LucasGabrielfl0/Cubesat-Hardware/Kicad_Libraries/Models_3D/STM32F411CEU6/BlackPill_F401v31.step

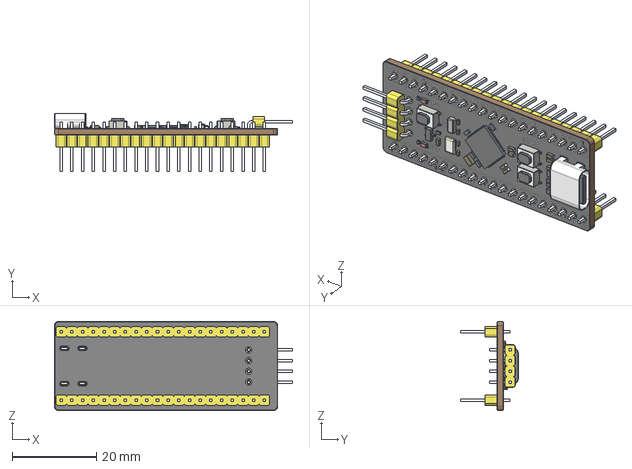
[picture p15: CAD file, 2026-04-24]
Kicad_Libraries/Models_3D/STM32F411CEU6/BlackPill_F401v31.step
56.5 x 13.7 x 21.2 mm
