LucasGabrielfl0/Cubesat-Hardware/Kicad_Libraries/Models_3D/Switch/ss12d06.stp

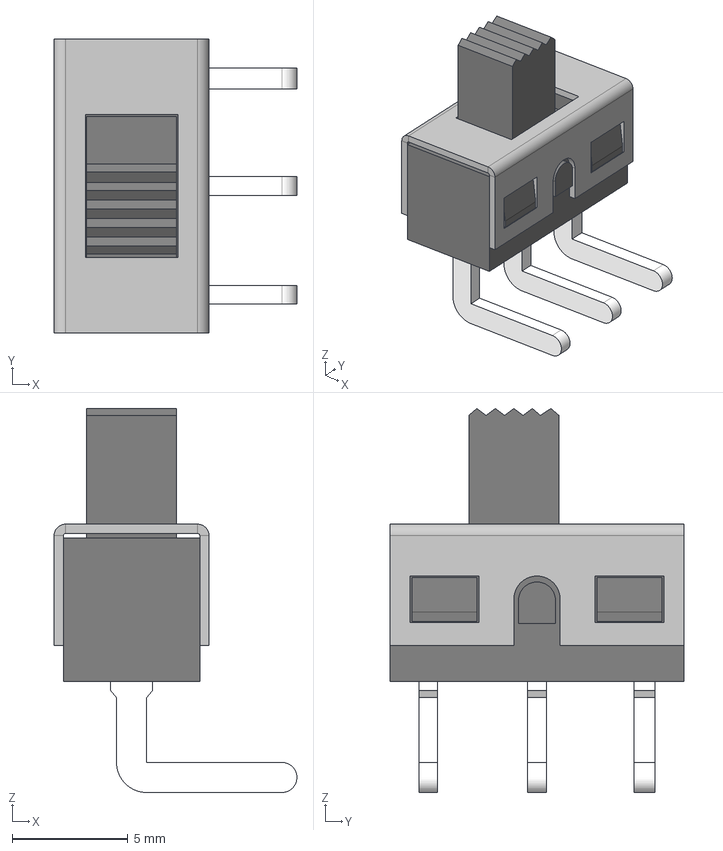
[picture p16: CAD file, 2026-06-01]
Kicad_Libraries/Models_3D/Switch/ss12d06.stp
10.5 x 12.7 x 16.6 mm
