LucasGabrielfl0/Cubesat-Hardware/Kicad_Libraries/Models_3D/Buck_Converter/XL4015 StepDown DC-DC 5A (CC-CV) v1.step

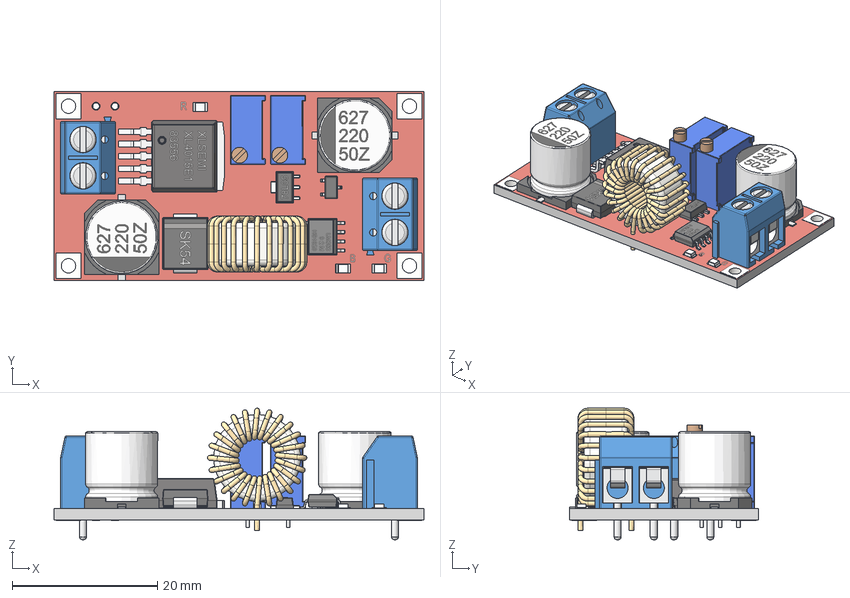
[picture p17: CAD file, 2026-05-25]
Kicad_Libraries/Models_3D/Buck_Converter/XL4015 StepDown DC-DC 5A (CC-CV) v1.step
51.0 x 26.0 x 18.1 mm
Basetta
DG301-5.0-02 v1 x 2
CAPACITOR 10x10 SMD v1 x 2
Trimpot 3296W v1 x 2
DO-214AB v1
XL4015 TO263-5-1 v1
LM358 SOIC08 v1
Toro
Spira x 22
SpiraCodA
SpiraCpdB
UPC78L08T-E1-AZ
SC-59A v1
LED v1 x 3
