LucasGabrielfl0/Cubesat-Hardware/Kicad_Libraries/Models_3D/Electrolytic_Capacitor/Electrolytic_Capacitor.step

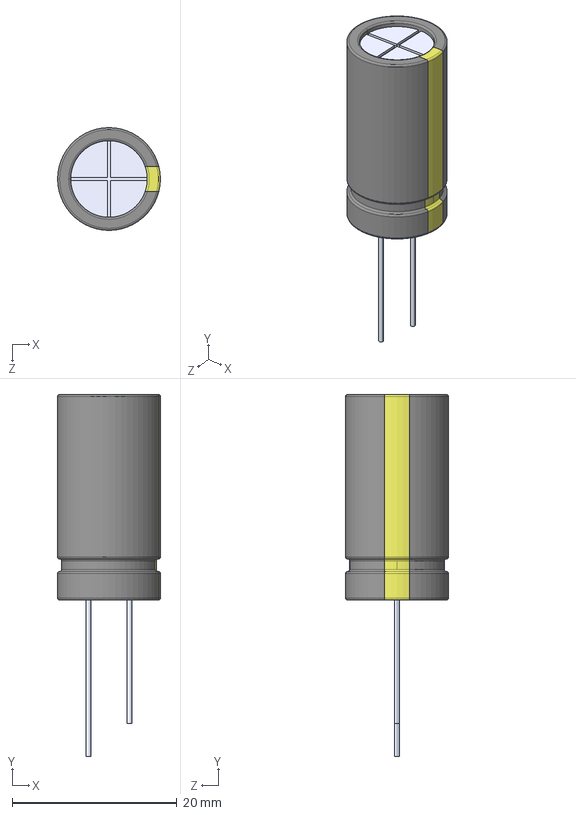
[picture p18: CAD file, 2026-05-12]
Kicad_Libraries/Models_3D/Electrolytic_Capacitor/Electrolytic_Capacitor.step
12.5 x 44.0 x 12.5 mm
