LucasGabrielfl0/Cubesat-Hardware/Kicad_Libraries/Models_3D/GPS_NEO6M/GY-NEO6MV2-noAnt.step

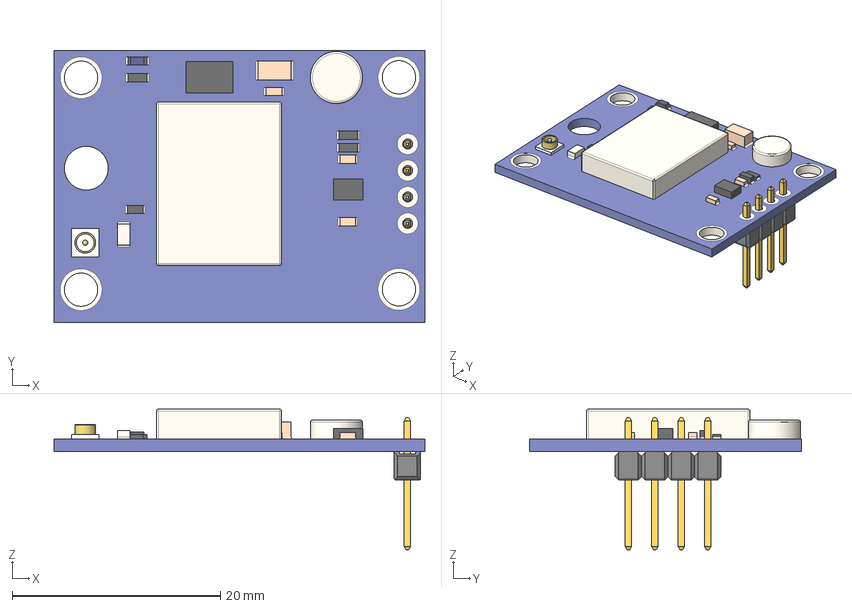
[picture p19: CAD file, 2026-04-24]
Kicad_Libraries/Models_3D/GPS_NEO6M/GY-NEO6MV2-noAnt.step
35.6 x 26.1 x 13.5 mm
Pin Header 1x4 TH Pitch 2.54mm
