LucasGabrielfl0/Cubesat-Hardware/Kicad_Libraries/Models_3D/Others/SS12D10_90_Degree.STEP

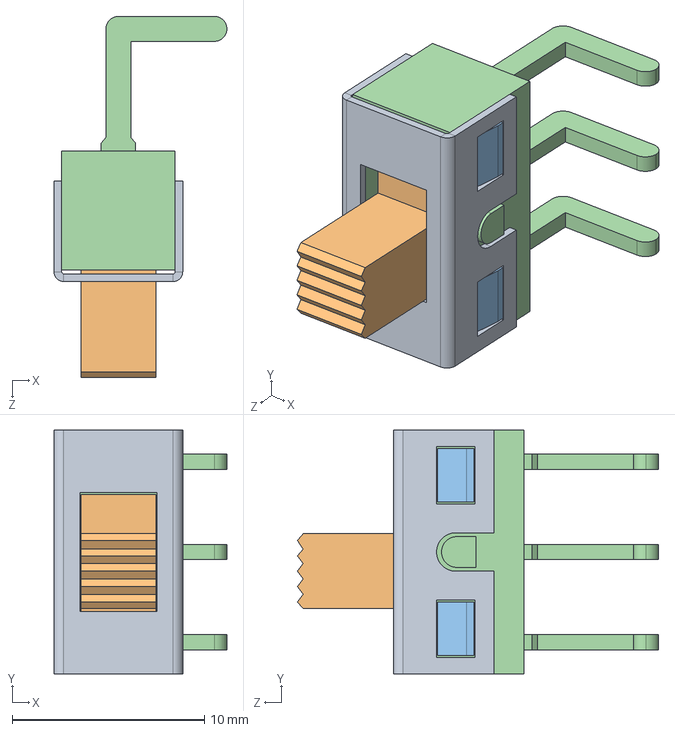
[picture p20: CAD file, 2026-05-26]
Kicad_Libraries/Models_3D/Others/SS12D10_90_Degree.STEP
9.00 x 12.7 x 18.8 mm
