LucasGabrielfl0/Cubesat-Hardware/Kicad_Libraries/Models_3D/BATTERY_PACK_18650/Hold_18650-4p_smd.stp

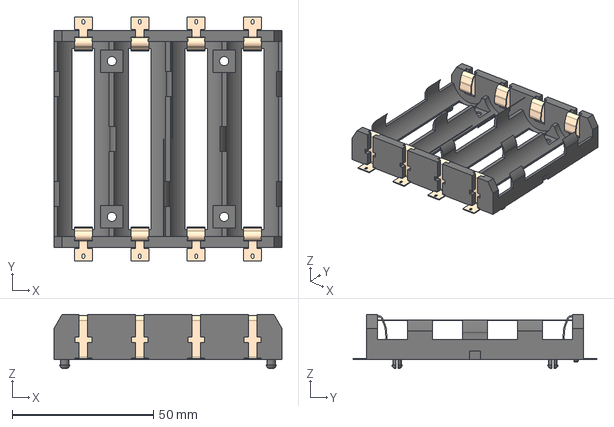
[picture p21: CAD file, 2026-04-24]
Kicad_Libraries/Models_3D/BATTERY_PACK_18650/Hold_18650-4p_smd.stp
80.8 x 86.4 x 19.3 mm
