LucasGabrielfl0/Cubesat-Hardware/Kicad_Libraries/Models_3D/Buck_Converter/LM2596 DC-DC Buck Converter Module.stp

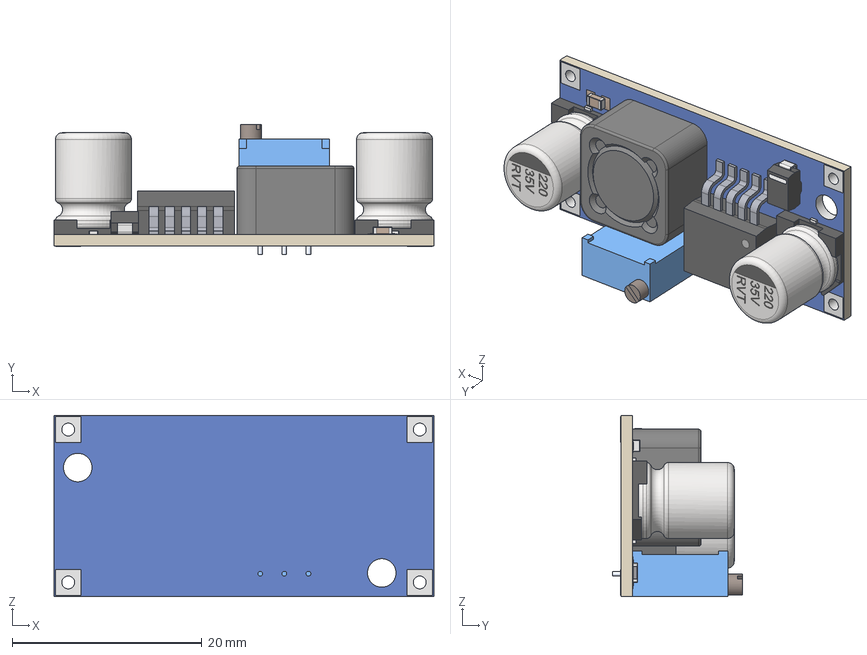
[picture p22: CAD file, 2026-04-24]
Kicad_Libraries/Models_3D/Buck_Converter/LM2596 DC-DC Buck Converter Module.stp
40.0 x 13.7 x 19.1 mm
CAPSMD220-35 x 2
Diode SMA
solder_hole x 4
