LucasGabrielfl0/Cubesat-Hardware/Kicad_Libraries/Models_3D/Electrolytic_Capacitor/0.22uF 50V electr 5 x11mm -P.diameter 2.5 mm-Black-White.stp

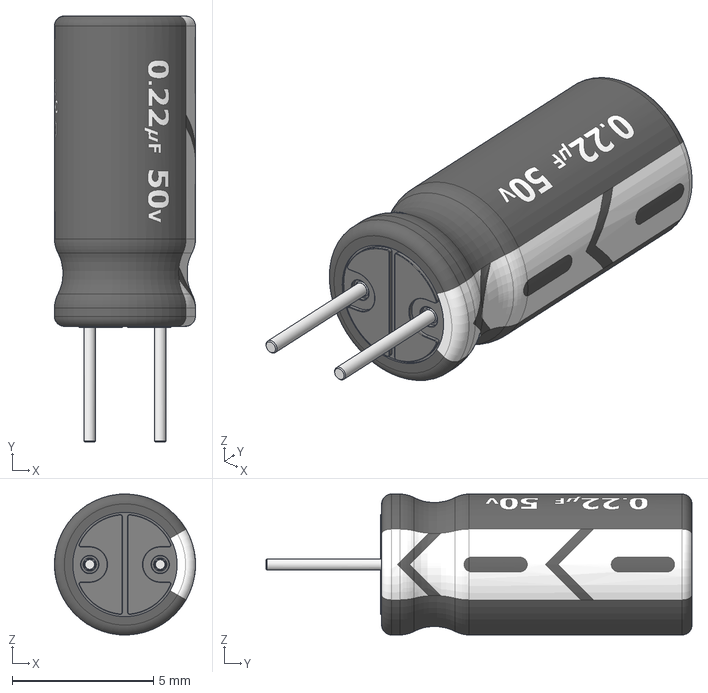
[picture p23: CAD file, 2026-05-12]
Kicad_Libraries/Models_3D/Electrolytic_Capacitor/0.22uF 50V electr 5 x11mm -P.diameter 2.5 mm-Black-White.stp
5.00 x 15.1 x 4.99 mm
