LucasGabrielfl0/Cubesat-Hardware/Kicad_Libraries/Models_3D/BATTERY_PACK_18650/Battery18650_2S.step

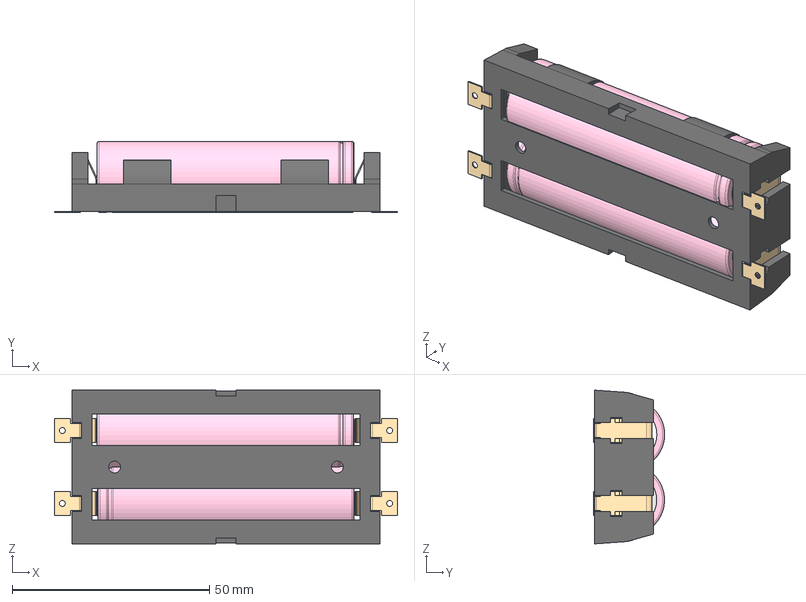
[picture p24: CAD file, 2026-04-24]
Kicad_Libraries/Models_3D/BATTERY_PACK_18650/Battery18650_2S.step
87.0 x 18.1 x 39.0 mm
Battery Holder
Battery-Holder_Metal-Lead x 4
