LucasGabrielfl0/Cubesat-Hardware/Kicad_Libraries/Models_3D/Others/kcd1_a.step

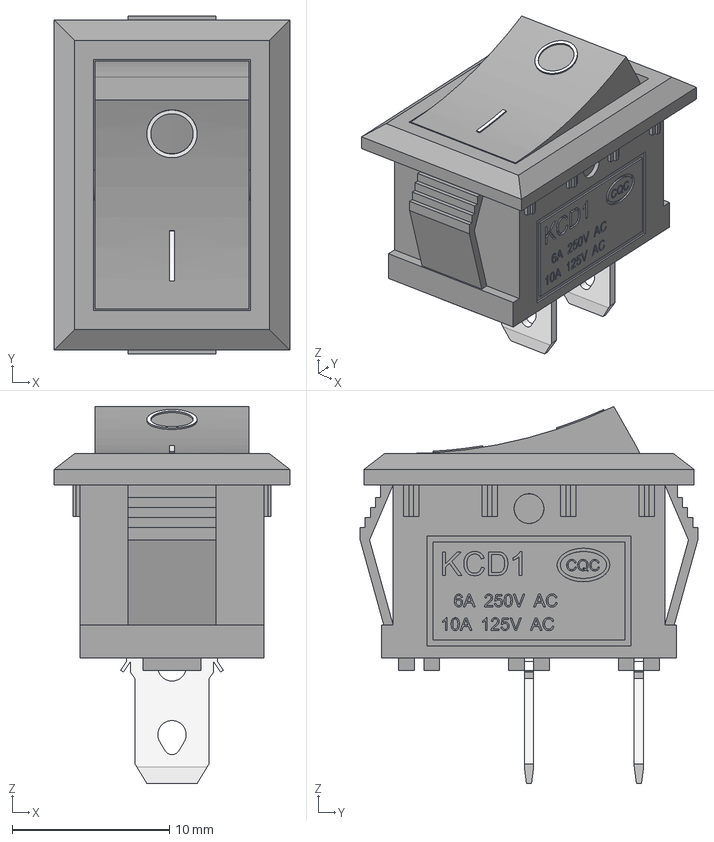
[picture p25: CAD file, 2026-05-25]
Kicad_Libraries/Models_3D/Others/kcd1_a.step
15.0 x 21.5 x 24.0 mm
Blade_001
Blade_002
Base_w_text
knob001
