LucasGabrielfl0/Cubesat-Hardware/Kicad_Libraries/Models_3D/Others/LED 3mm Blue 21mm Leads.step

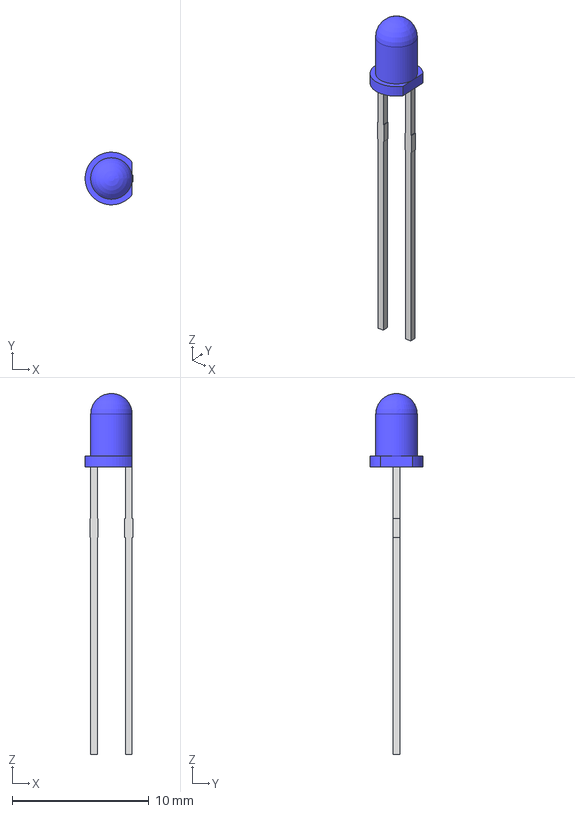
[picture p26: CAD file, 2026-05-12]
Kicad_Libraries/Models_3D/Others/LED 3mm Blue 21mm Leads.step
3.50 x 3.85 x 26.4 mm
LEDBody
Lead1Body
Lead2Body
