LucasGabrielfl0/Cubesat-Hardware/Kicad_Libraries/Models_3D/BATTERY_PACK_18650/BatteryPack_4S.step

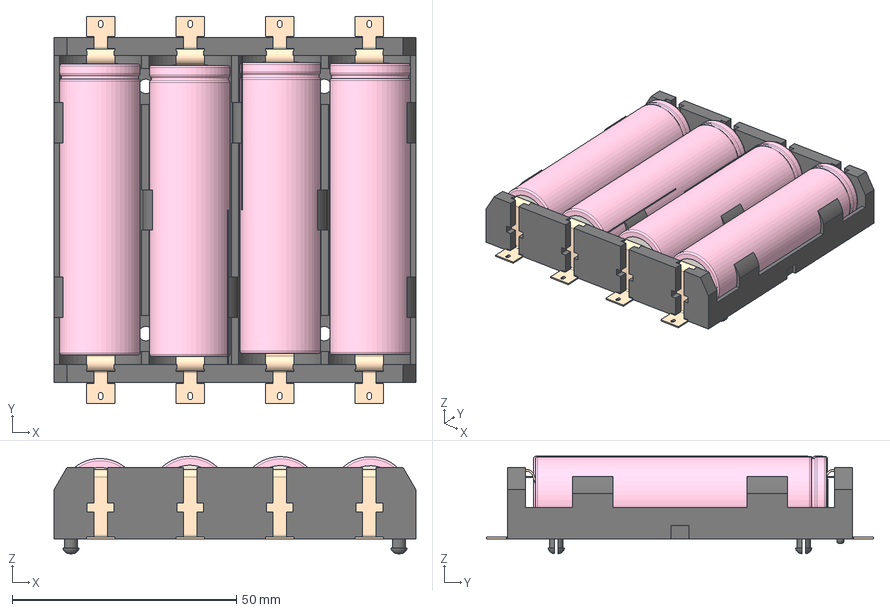
[picture p27: CAD file, 2026-04-24]
Kicad_Libraries/Models_3D/BATTERY_PACK_18650/BatteryPack_4S.step
80.8 x 86.4 x 21.8 mm
Hold_18650_Con_smd x 8
Hold_18650-4p_smd
