LucasGabrielfl0/Cubesat-Hardware/Kicad_Libraries/Models_3D/Others/Led 5mm green_.step

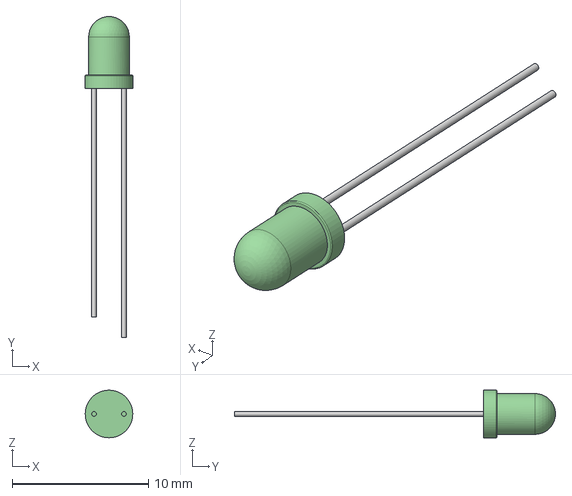
[picture p28: CAD file, 2026-04-24]
Kicad_Libraries/Models_3D/Others/Led 5mm green_.step
3.50 x 23.6 x 3.50 mm
