LucasGabrielfl0/Cubesat-Hardware/Kicad_Libraries/Models_3D/BATTERY_PACK_18650/BLM Blossom Electronics STM THM FOR 18650 Battery Holder With Battery V1.2.STEP

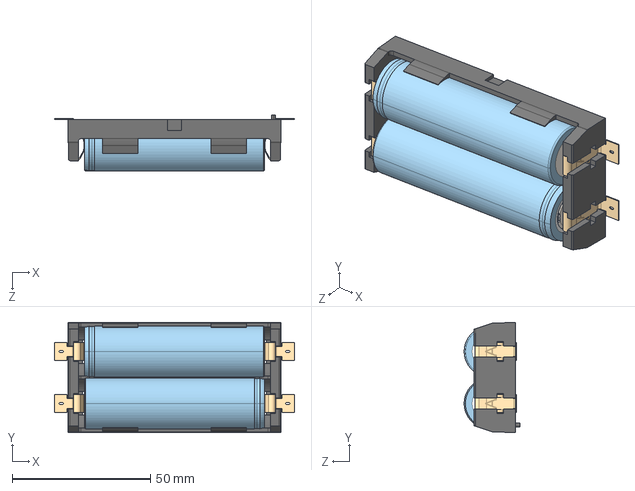
[picture p29: CAD file, 2026-04-24]
Kicad_Libraries/Models_3D/BATTERY_PACK_18650/BLM Blossom Electronics STM THM FOR 18650 Battery Holder With Battery V1.2.STEP
86.8 x 39.8 x 20.2 mm
