LucasGabrielfl0/Cubesat-Hardware/Kicad_Libraries/Models_3D/Others/Led 5mm red_.step

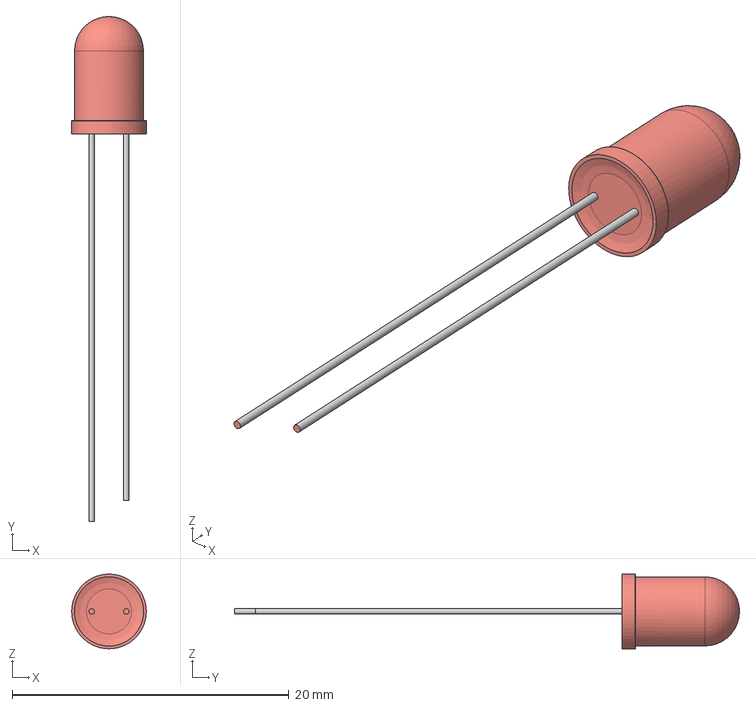
[picture p30: CAD file, 2026-04-24]
Kicad_Libraries/Models_3D/Others/Led 5mm red_.step
5.40 x 36.5 x 5.39 mm
