LucasGabrielfl0/Cubesat-Hardware/Kicad_Libraries/Models_3D/Others/Wippschalter Rund - BG.STEP

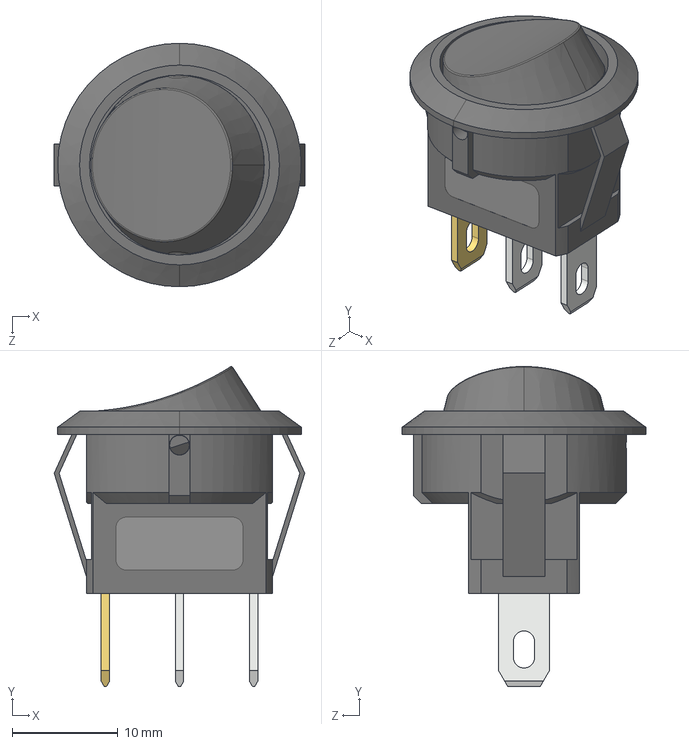
[picture p31: CAD file, 2026-04-24]
Kicad_Libraries/Models_3D/Others/Wippschalter Rund - BG.STEP
23.7 x 30.2 x 23.0 mm
Wippschalter Rund - T2
Wippschalter Rund - T1
